bu-cisl/Computational-Miniature-Mesoscope-CM2/CAD_models/CM2_V1/mla_housing.stl

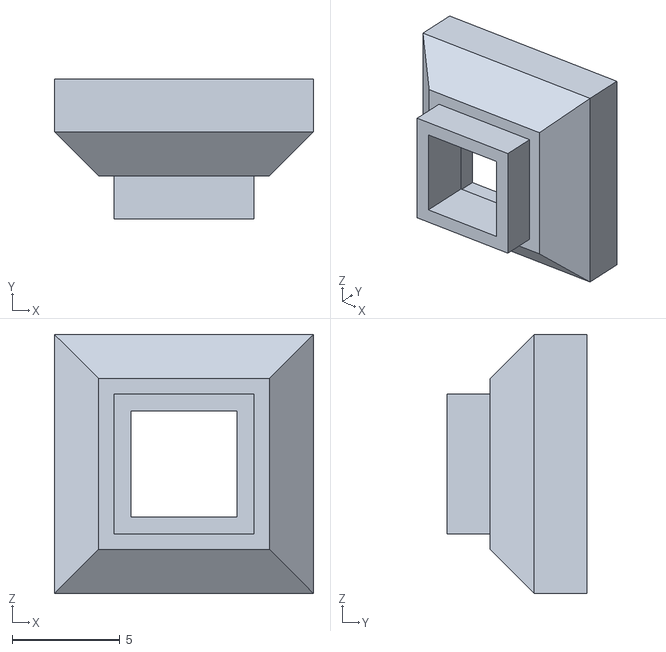
[picture p23: CAD file, 2022-04-20, an earlier design]
CAD_models/CM2_V1/mla_housing.stl
12.0 x 6.50 x 12.0
