bu-cisl/Computational-Miniature-Mesoscope-CM2/Zemax_models/CM2_V1/zemax_mla_aperture.stl

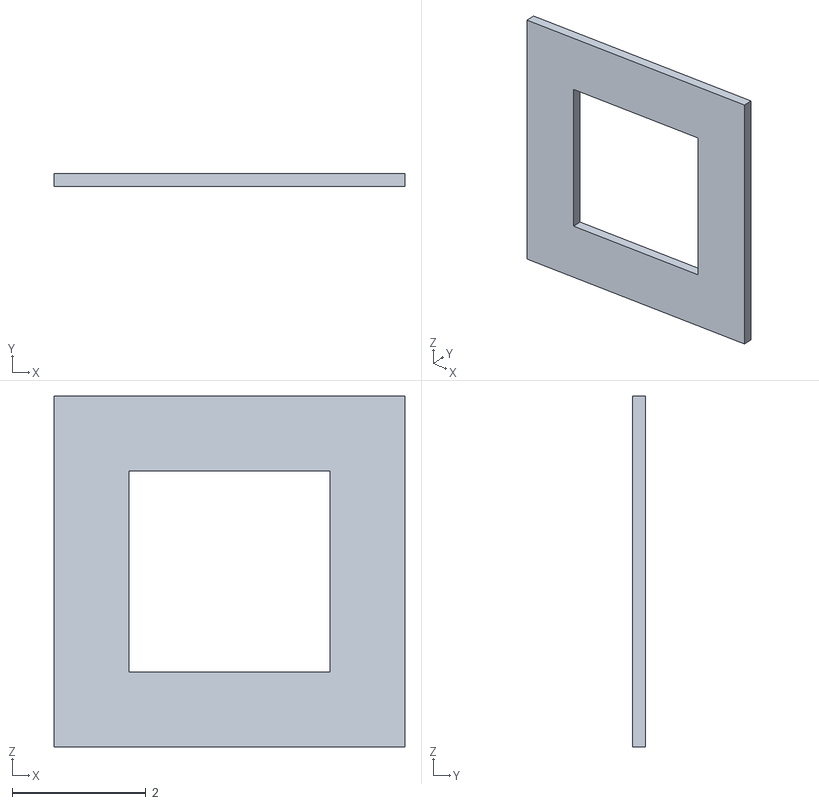
[picture p24: CAD file, 2022-04-20, an earlier design]
Zemax_models/CM2_V1/zemax_mla_aperture.stl
5.25 x 0.2 x 5.25
