bu-cisl/Computational-Miniature-Mesoscope-CM2/CAD_models/CM2_V1/led_housing.stl

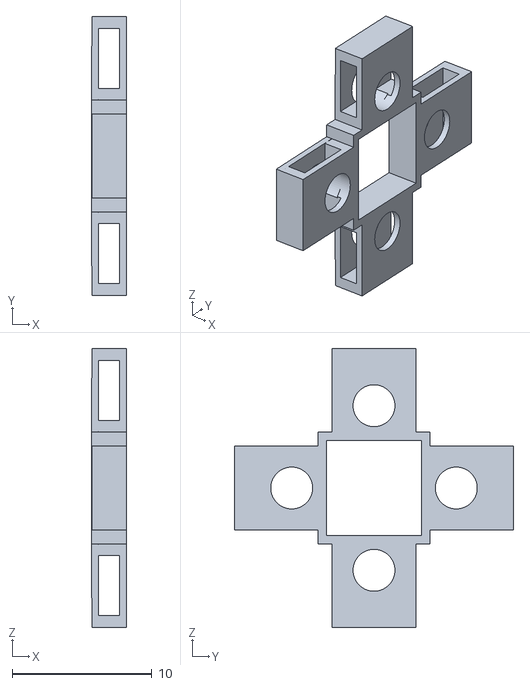
[picture p25: CAD file, 2022-04-20, an earlier design]
CAD_models/CM2_V1/led_housing.stl
2.50 x 20.0 x 20.0
